Vitorbnc/ender3_addons/Laser Engraving Module/nubm08 laser diode pinout.png

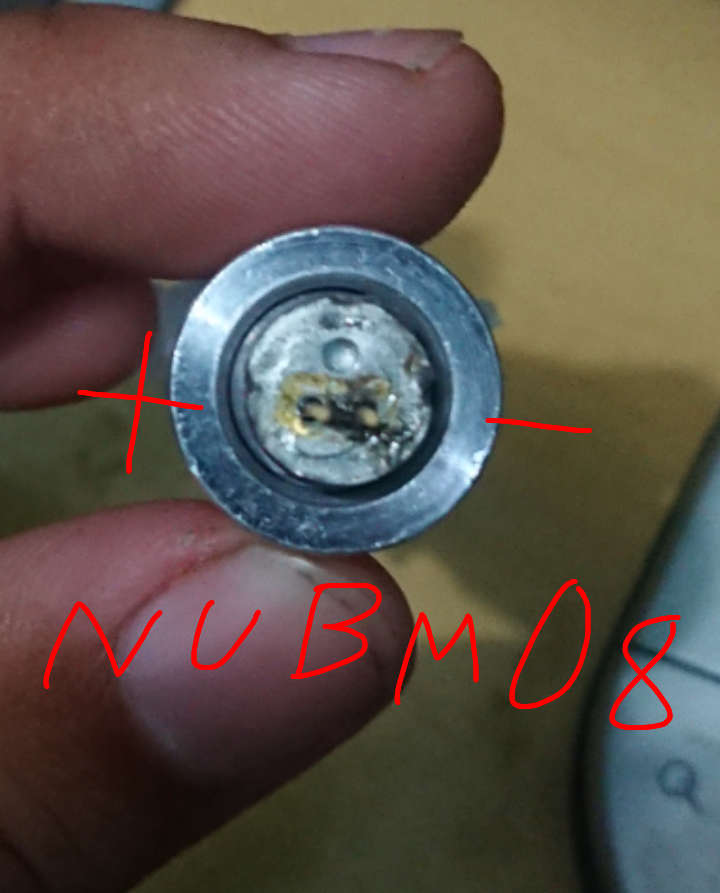
Laser Engraving Module/nubm08 laser diode pinout.png
