Vitorbnc/ender3_addons/Fresa CNC para Impressora 3D/broca pcb.jpg

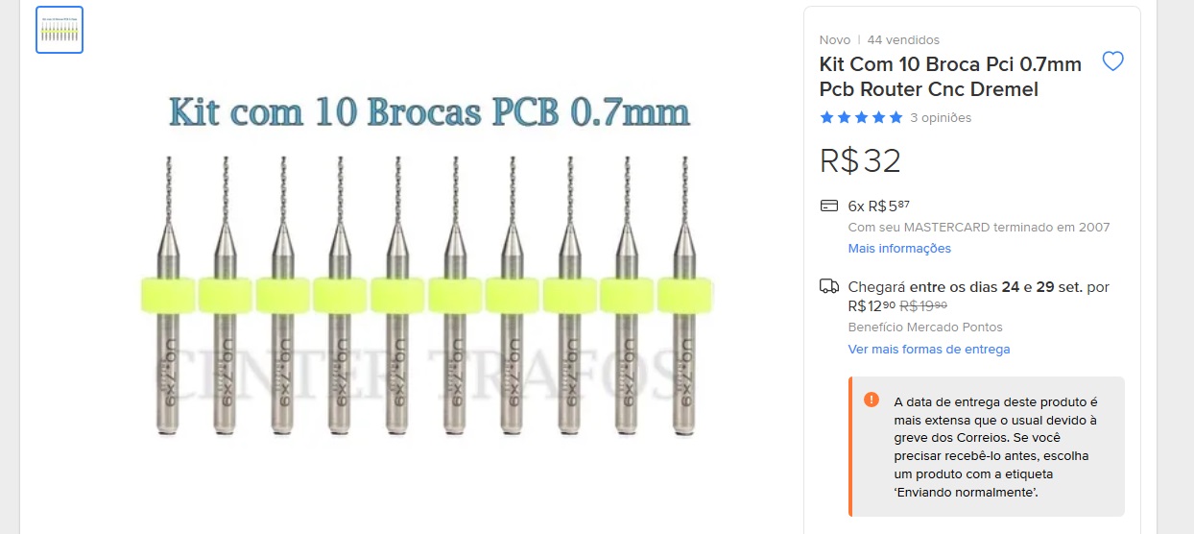
Fresa CNC para Impressora 3D/broca pcb.jpg
