Vitorbnc/ender3_addons/Fresa CNC para Impressora 3D/cnc tool home.png

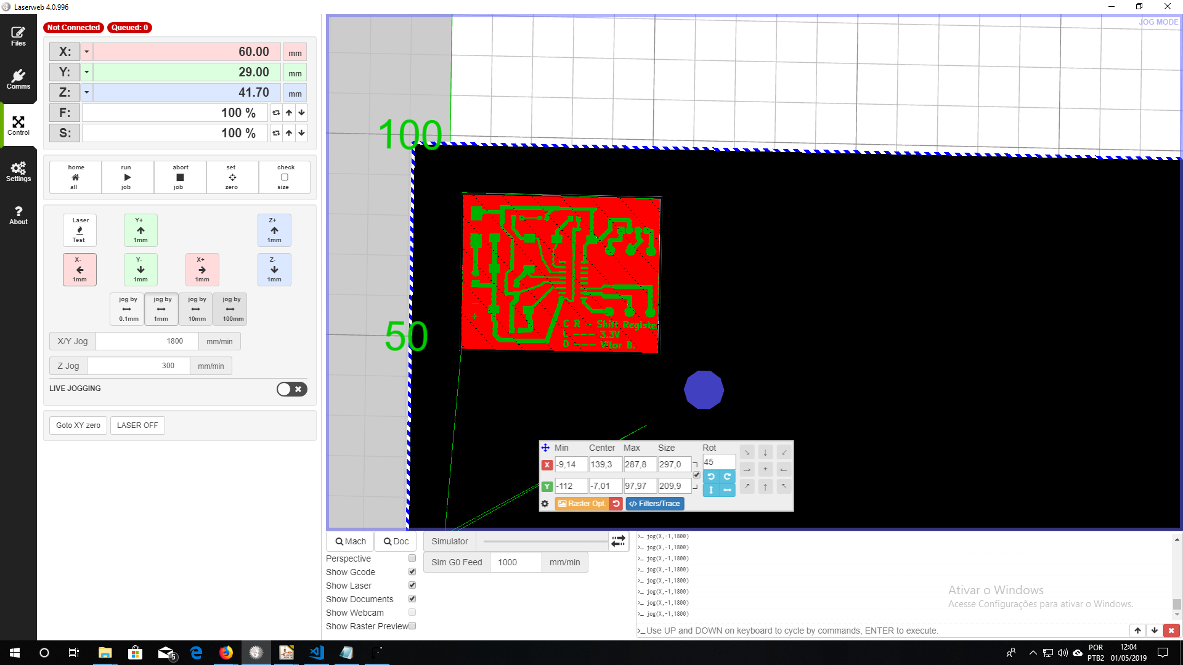
Fresa CNC para Impressora 3D/cnc tool home.png
