Vitorbnc/ender3_addons/Fresa CNC para Impressora 3D/compressor.png

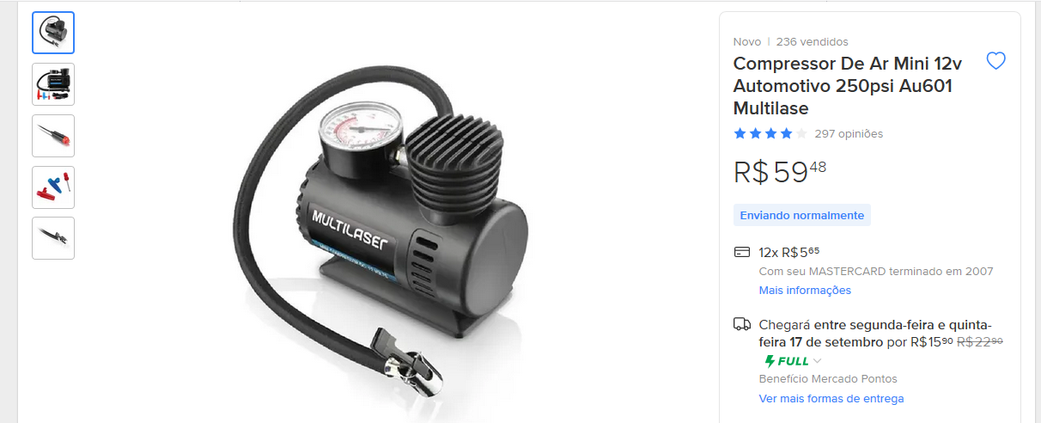
Fresa CNC para Impressora 3D/compressor.png
