Vitorbnc/ender3_addons/Fresa CNC para Impressora 3D/DSC_0071.JPG

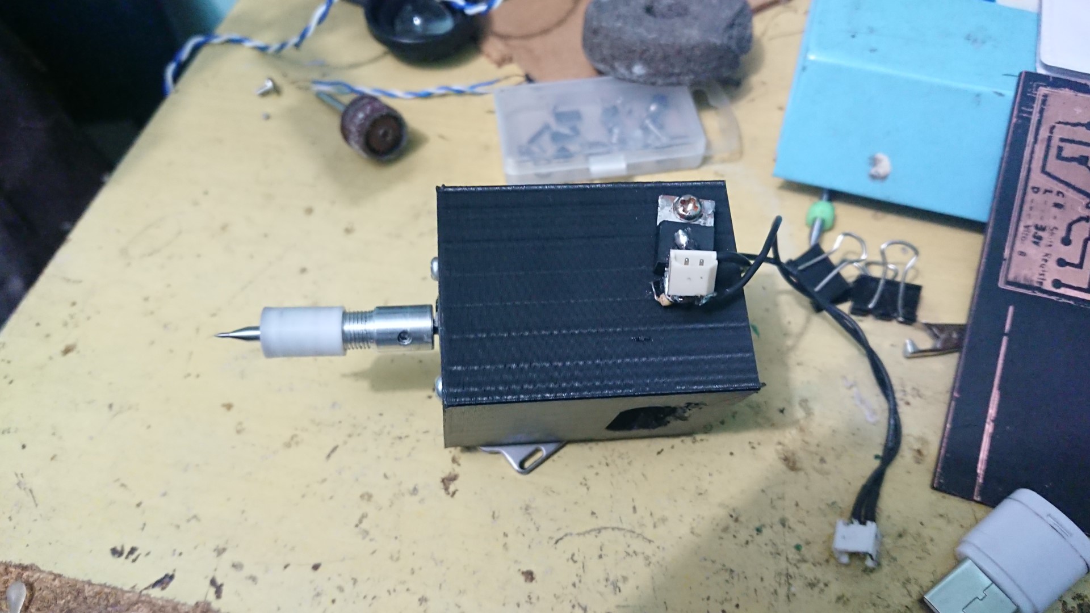
Fresa CNC para Impressora 3D/DSC_0071.JPG
