Vitorbnc/ender3_addons/Fresa CNC para Impressora 3D/DSC_0634.jpg

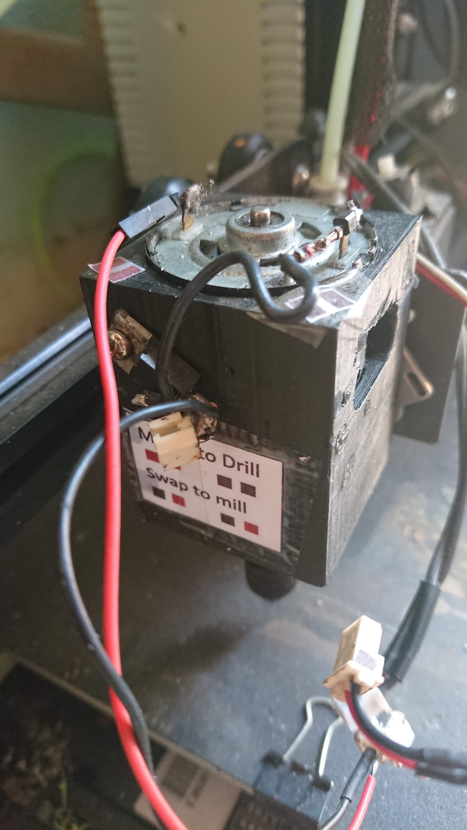
Fresa CNC para Impressora 3D/DSC_0634.jpg
