Vitorbnc/ender3_addons/Fresa CNC para Impressora 3D/Furos FlatCam/Flatcam settings.png

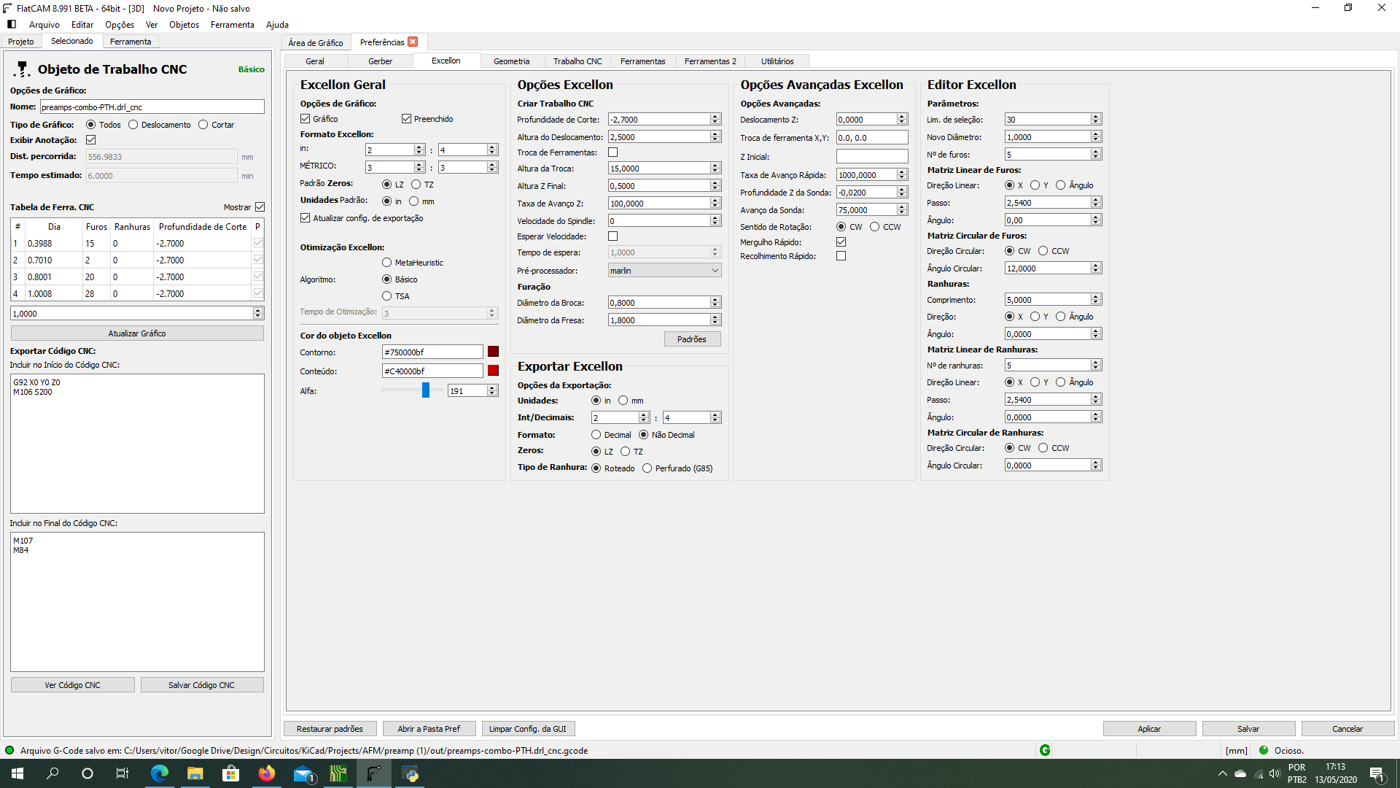
Fresa CNC para Impressora 3D/Furos FlatCam/Flatcam settings.png
