Vitorbnc/ender3_addons/Fresa CNC para Impressora 3D/generate drill file kicad.png

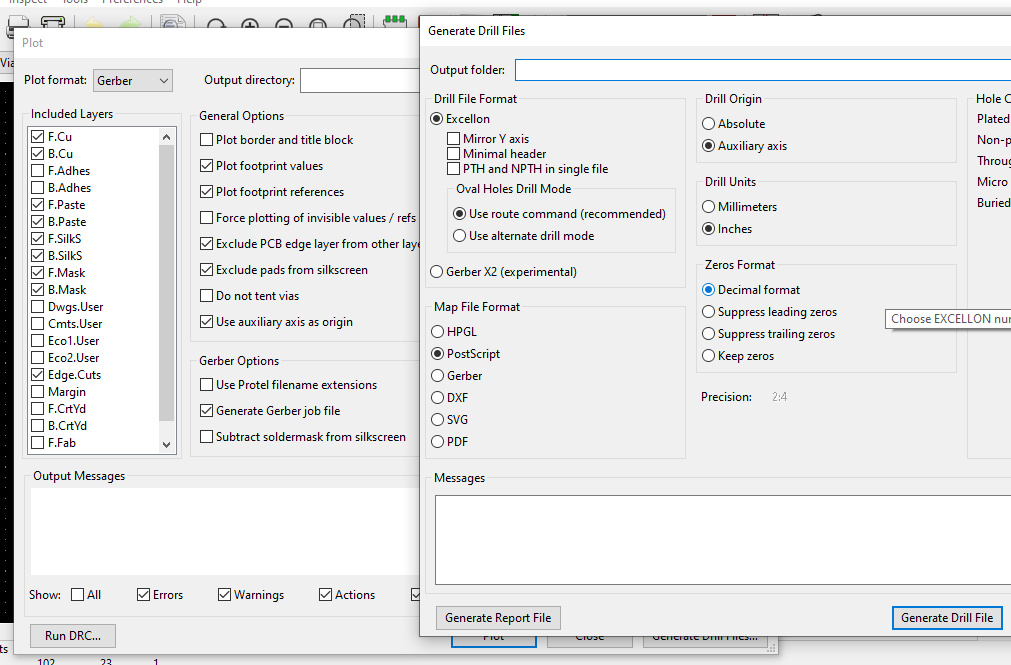
Fresa CNC para Impressora 3D/generate drill file kicad.png
