Vitorbnc/ender3_addons/Fresa CNC para Impressora 3D/import excellon flatcam.png

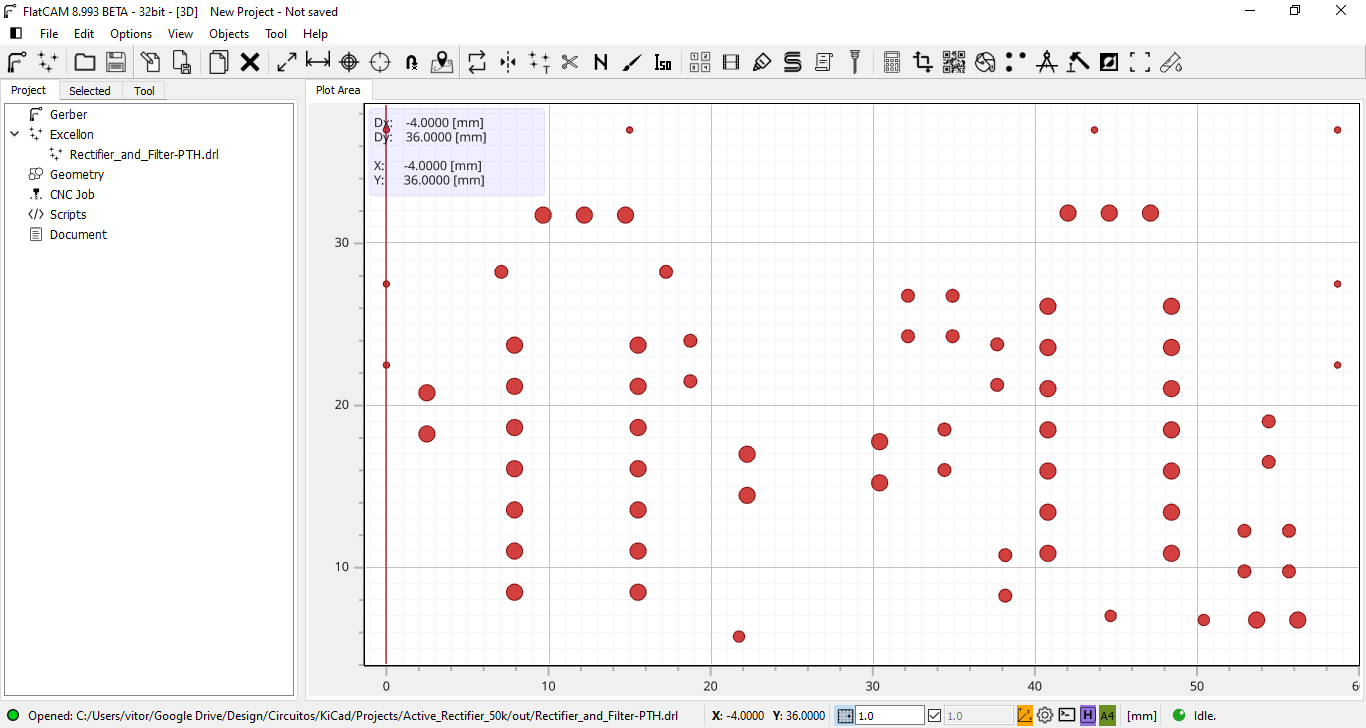
Fresa CNC para Impressora 3D/import excellon flatcam.png
