Vitorbnc/ender3_addons/Fresa CNC para Impressora 3D/mini mandril.png

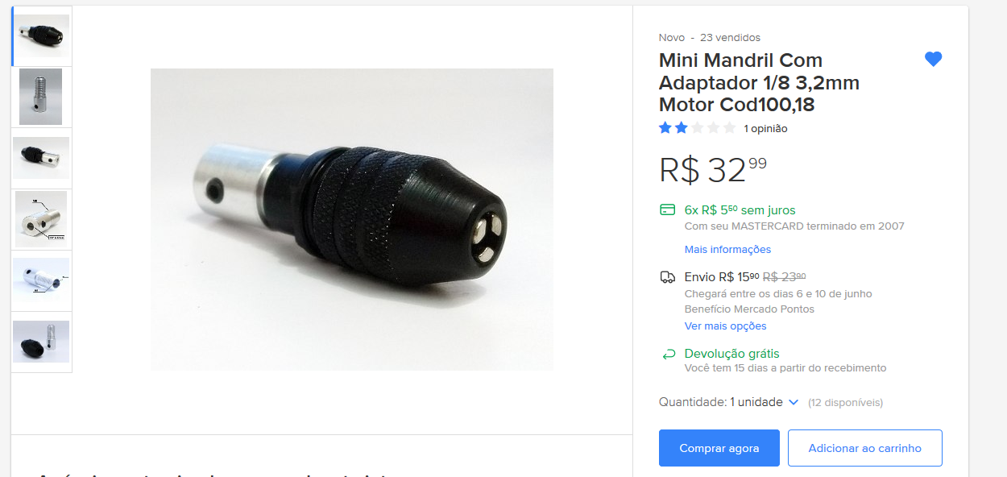
Fresa CNC para Impressora 3D/mini mandril.png
