Vitorbnc/ender3_addons/Fresa CNC para Impressora 3D/schematics.png

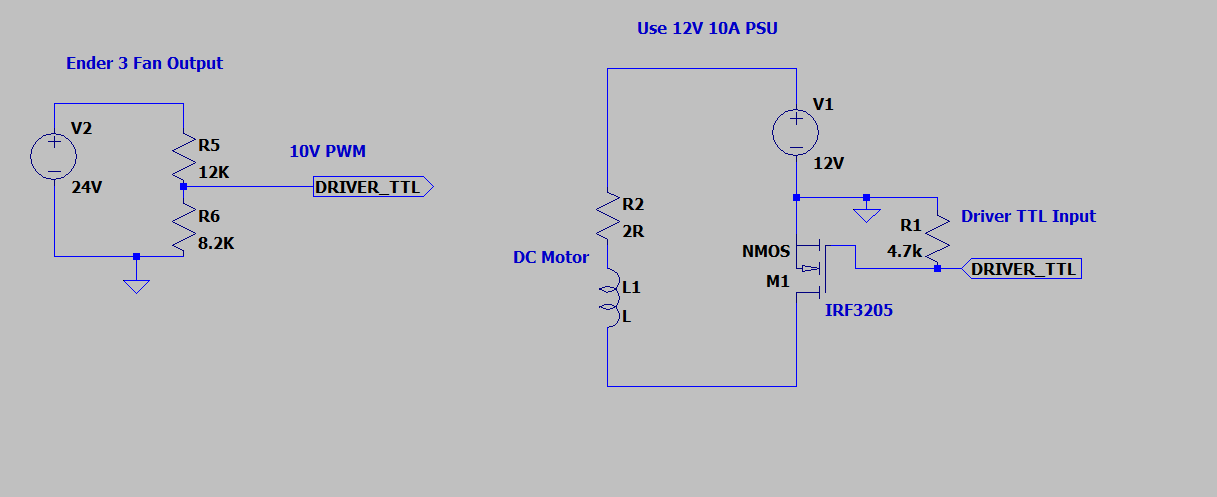
Fresa CNC para Impressora 3D/schematics.png
