Vitorbnc/ender3_addons/Laser Engraving Module/ender 3 laser pcb engraving zero position.png

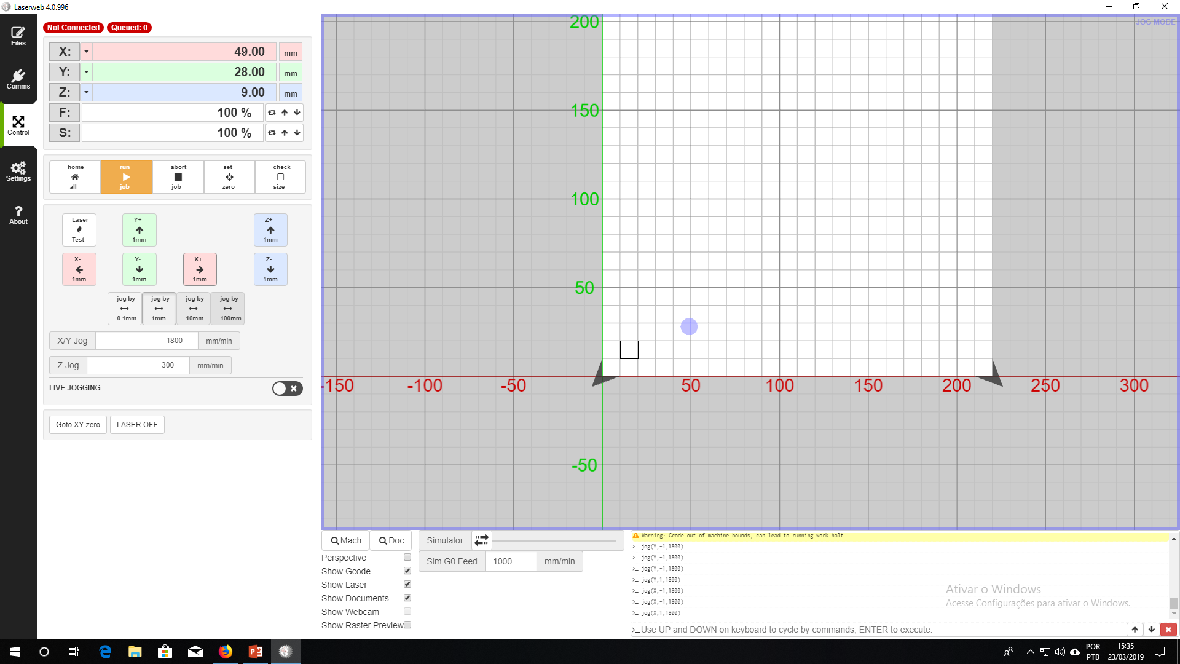
Laser Engraving Module/ender 3 laser pcb engraving zero position.png
