Vitorbnc/ender3_addons/Laser Engraving Module/Engraving Parameters/Params -  laser grbl madeira.png

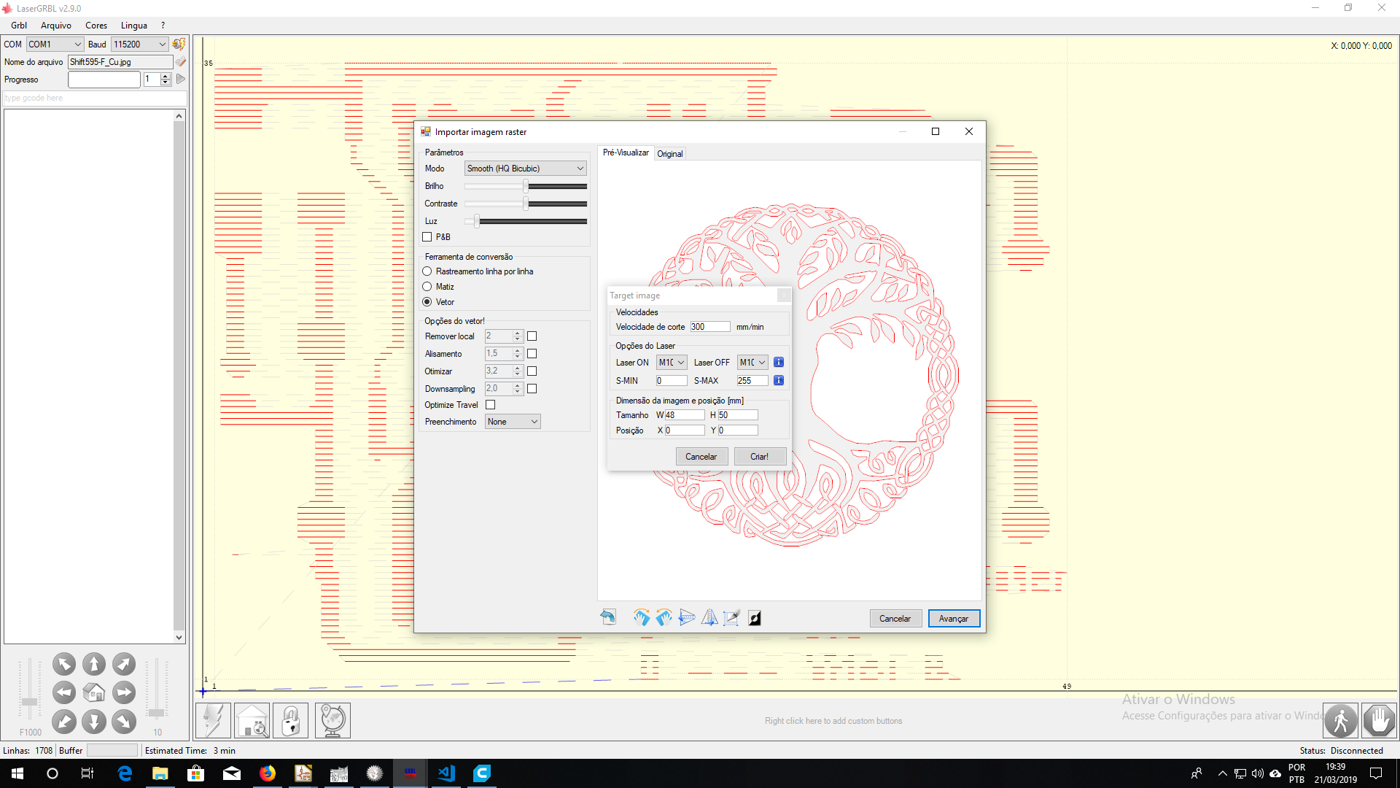
Laser Engraving Module/Engraving Parameters/Params - laser grbl madeira.png
