Vitorbnc/ender3_addons/Laser Engraving Module/Engraving Parameters/Params - gravação em plástico ou couro 2.png

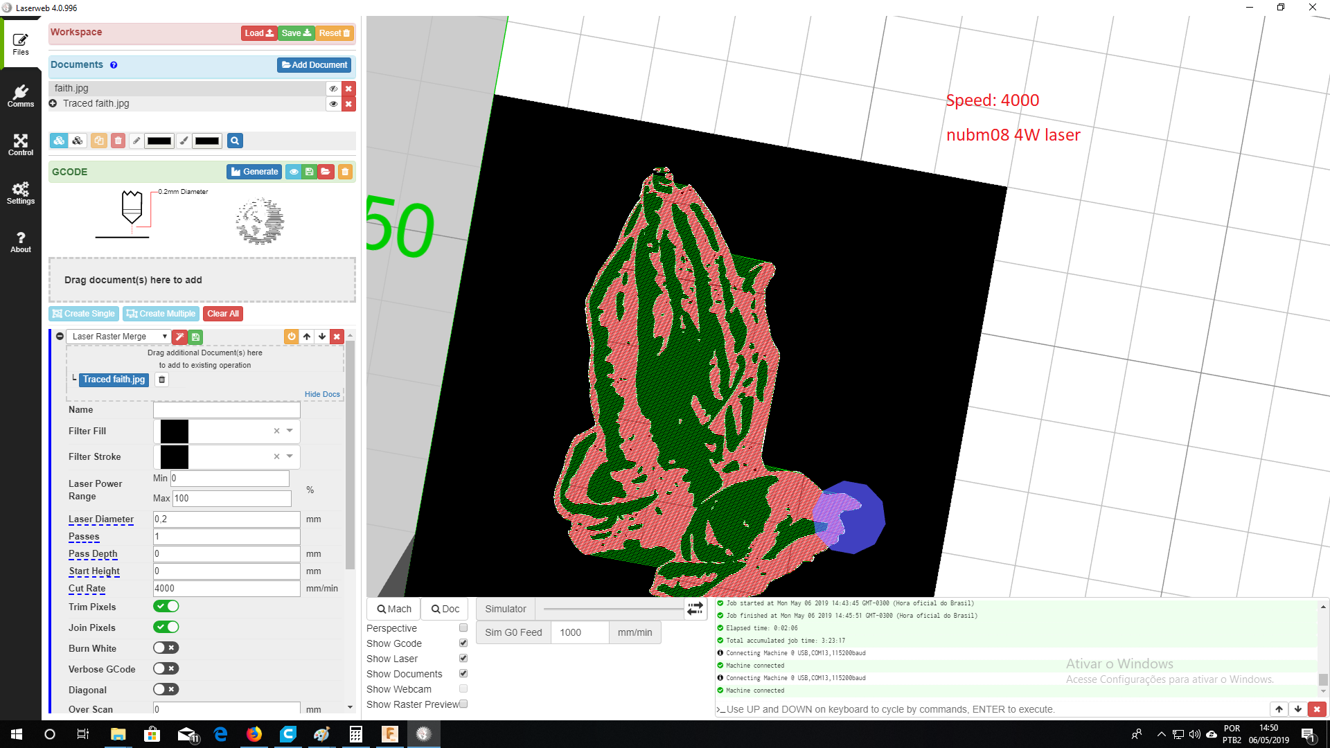
Laser Engraving Module/Engraving Parameters/Params - gravação em plástico ou couro 2.png
