Vitorbnc/ender3_addons/Laser Engraving Module/Engraving Parameters/Params - LaserWeb PCB Raster Settings.png

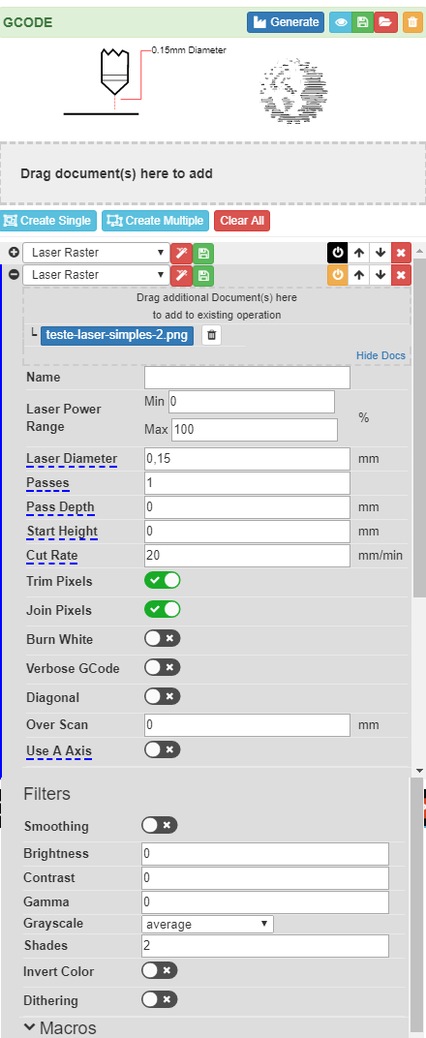
Laser Engraving Module/Engraving Parameters/Params - LaserWeb PCB Raster Settings.png
