Vitorbnc/ender3_addons/Laser Engraving Module/Fotos/Chaveamento com FET em paralelo - não mais usado.jpg

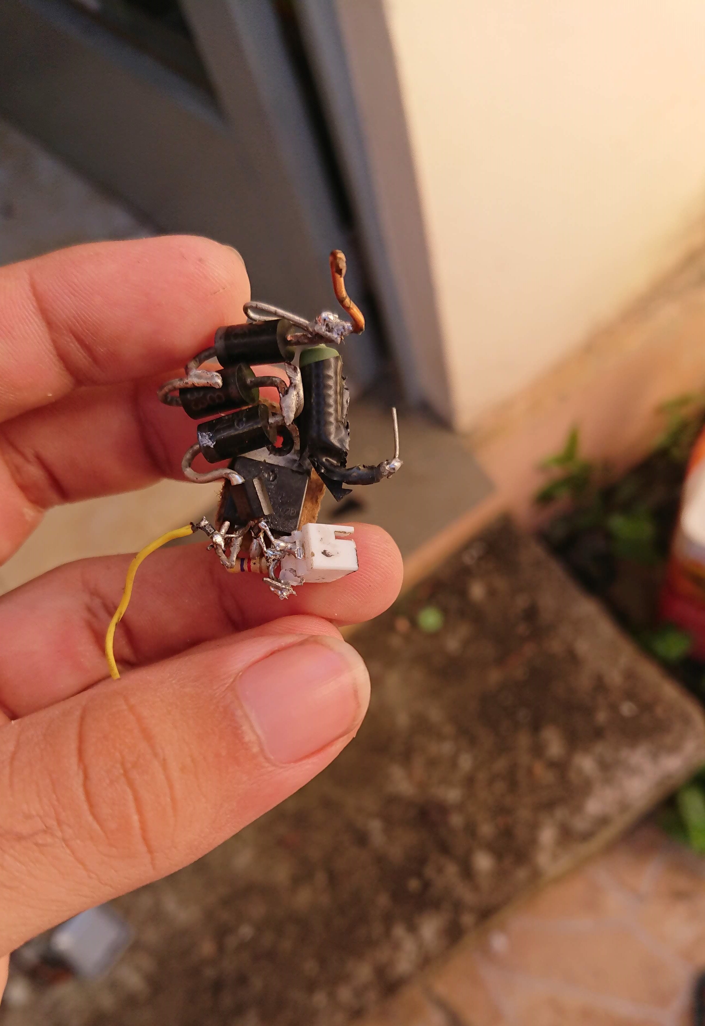
Laser Engraving Module/Fotos/Chaveamento com FET em paralelo - não mais usado.jpg
