Vitorbnc/ender3_addons/Laser Engraving Module/Fotos/DSC_0054.jpg

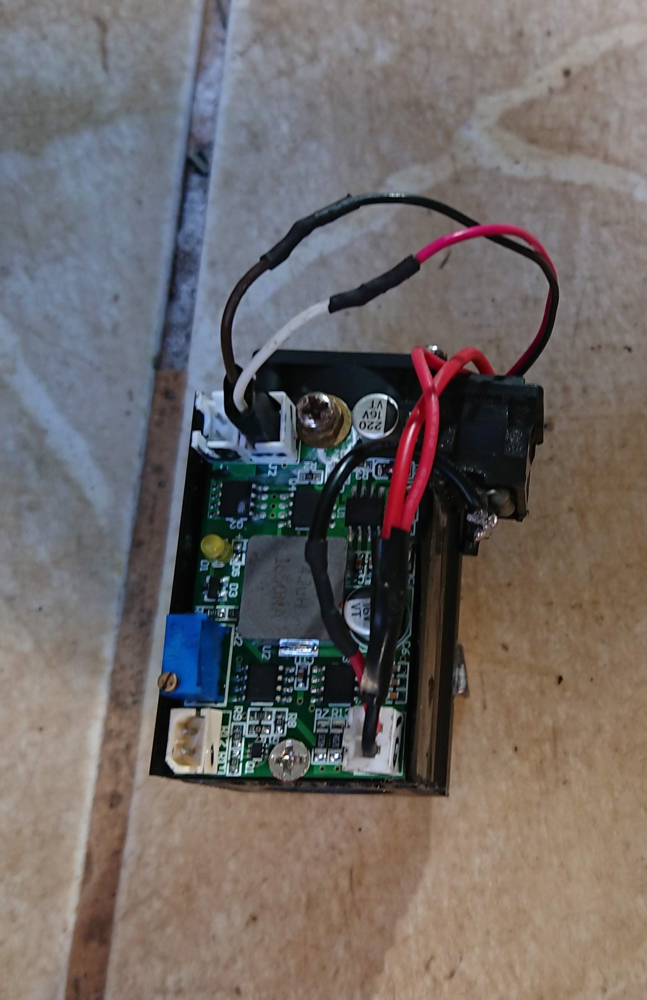
Laser Engraving Module/Fotos/DSC_0054.jpg
