Vitorbnc/ender3_addons/Laser Engraving Module/Fotos/DSC_0055.jpg

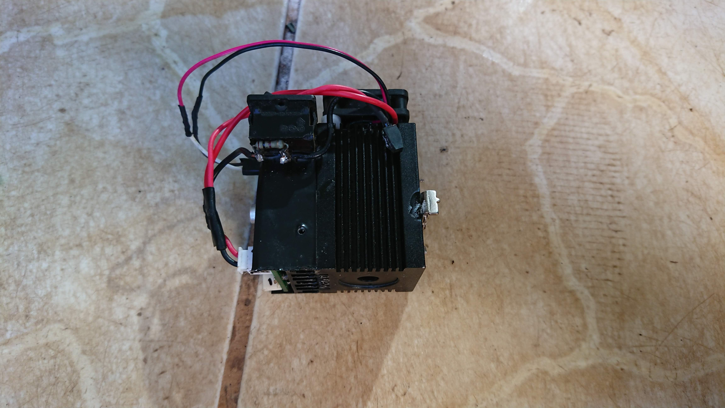
Laser Engraving Module/Fotos/DSC_0055.jpg
