Vitorbnc/ender3_addons/Laser Engraving Module/Fotos/DSC_0056.jpg

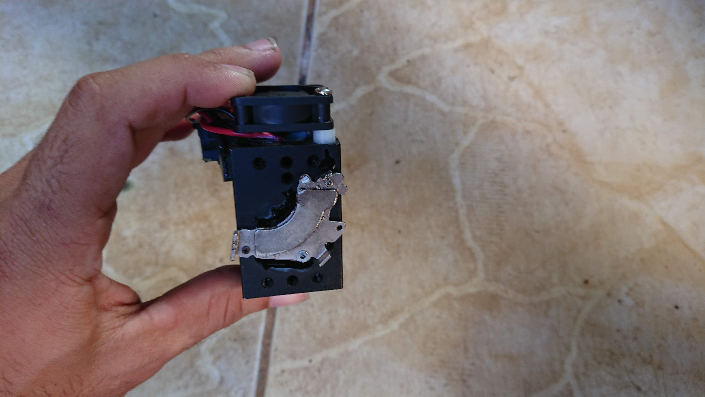
Laser Engraving Module/Fotos/DSC_0056.jpg
