Vitorbnc/ender3_addons/Laser Engraving Module/Fotos/DSC_0057.jpg

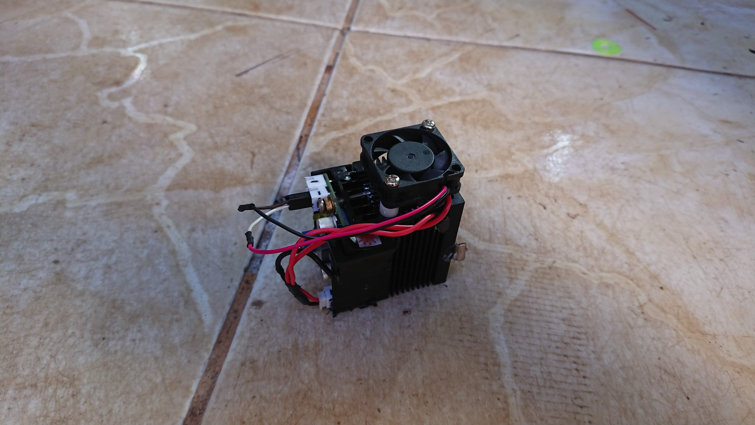
Laser Engraving Module/Fotos/DSC_0057.jpg
