Vitorbnc/ender3_addons/Laser Engraving Module/Fotos/version 2 (1).jpg

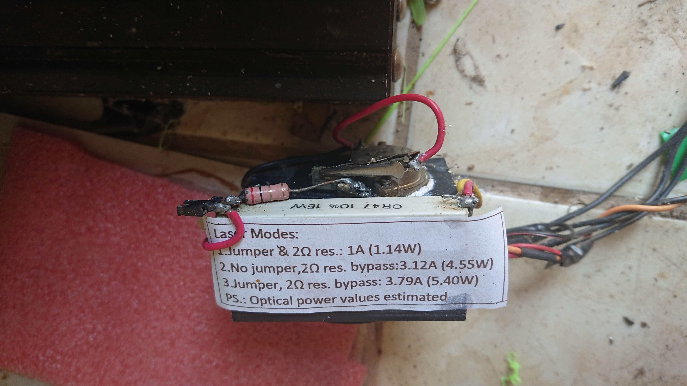
Laser Engraving Module/Fotos/version 2 (1).jpg
