Vitorbnc/ender3_addons/Laser Engraving Module/Gravação em Dry Film/Gravação em Dry Film PCB.JPG

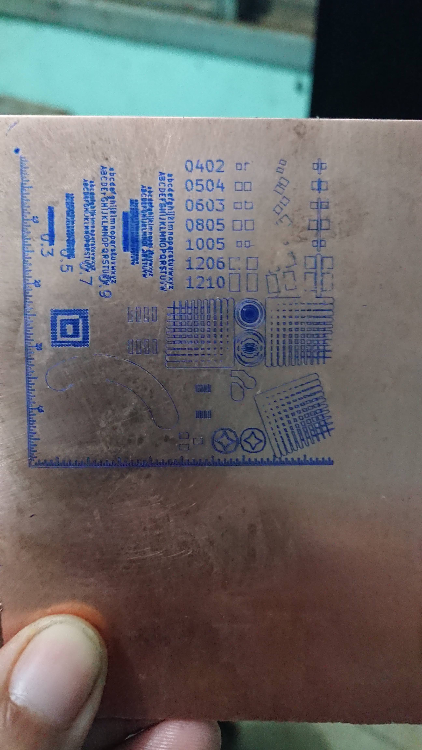
Laser Engraving Module/Gravação em Dry Film/Gravação em Dry Film PCB.JPG
