Vitorbnc/ender3_addons/Laser Engraving Module/Queimar tinta preta sobre PCB/Shift595 - Inf 1x 100, Sup - 1x200mmps - limpos.png

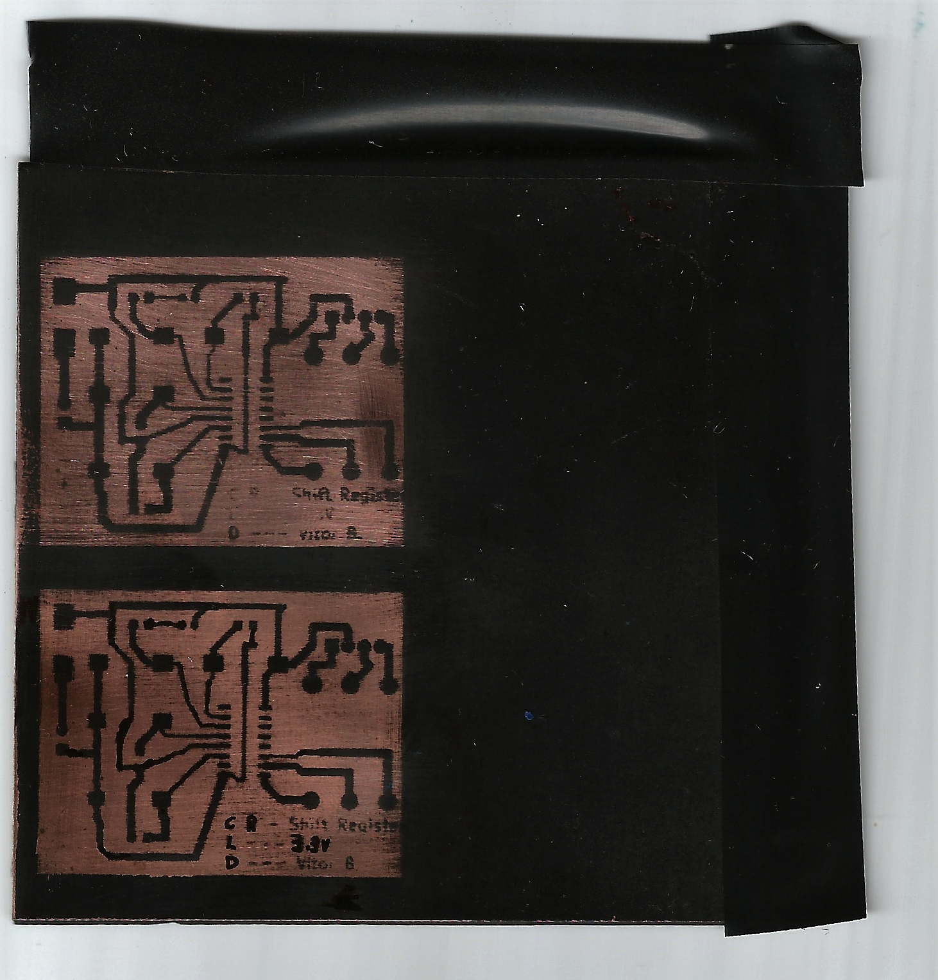
Laser Engraving Module/Queimar tinta preta sobre PCB/Shift595 - Inf 1x 100, Sup - 1x200mmps - limpos.png
