Vitorbnc/ender3_addons/Laser Engraving Module/Kit materiais laser.PNG

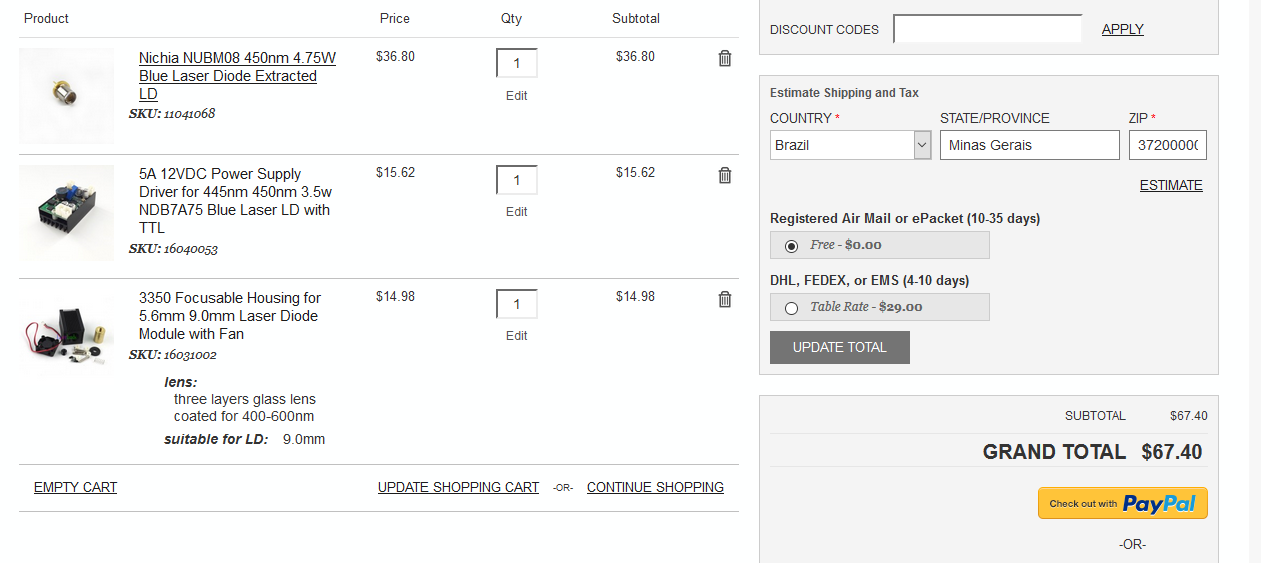
Laser Engraving Module/Kit materiais laser.PNG
