Vitorbnc/ender3_addons/Laser Engraving Module/Ender 3 Laser Wiring v1.png

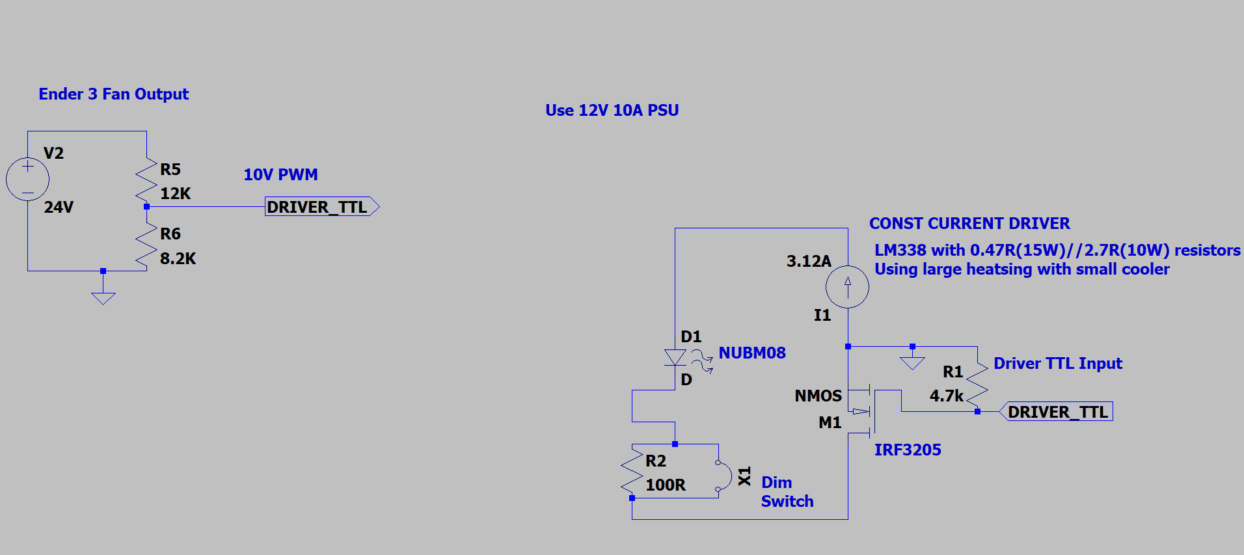
Laser Engraving Module/Ender 3 Laser Wiring v1.png
