Vitorbnc/ender3_addons/Laser Engraving Module/LEIA - Ender 3 Laser Wiring v1.png

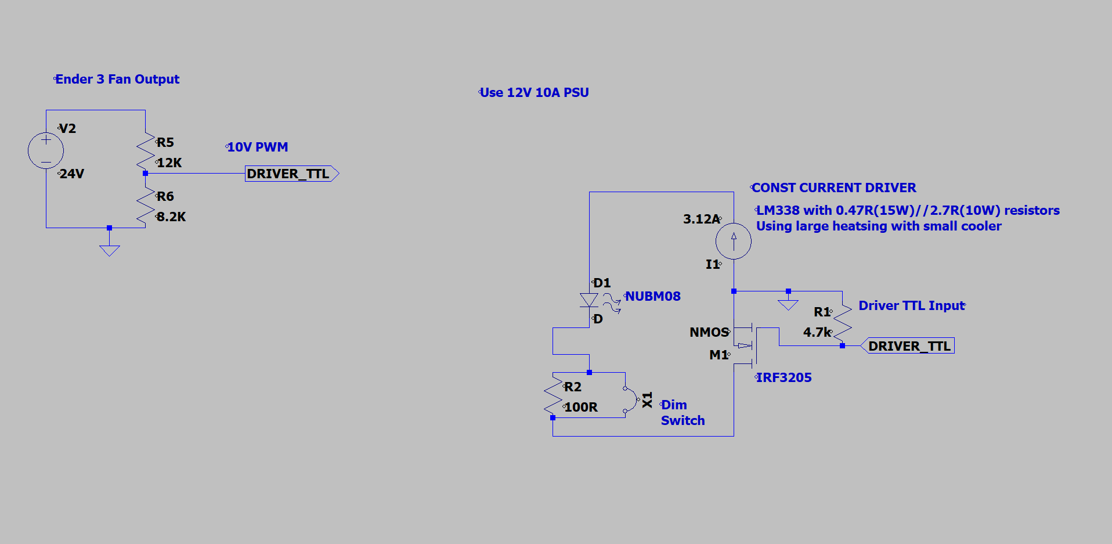
Laser Engraving Module/LEIA - Ender 3 Laser Wiring v1.png
