Vitorbnc/ender3_addons/Fresa CNC para Impressora 3D/teste_risca_tinta_pcb.JPG

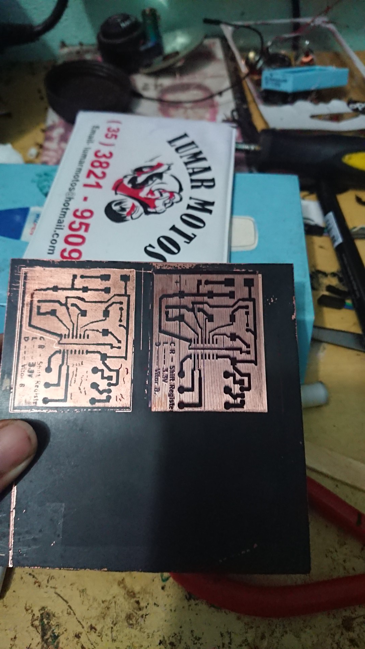
Fresa CNC para Impressora 3D/teste_risca_tinta_pcb.JPG
