Vitorbnc/ender3_addons/Laser Engraving Module/Imagens para teste/faith.jpg

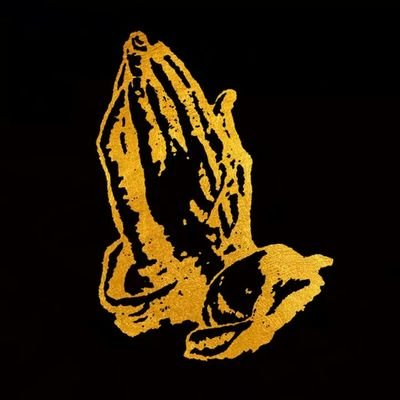
Laser Engraving Module/Imagens para teste/faith.jpg
