Vitorbnc/ender3_addons/Laser Engraving Module/Imagens para teste/yggdrasil.jpg

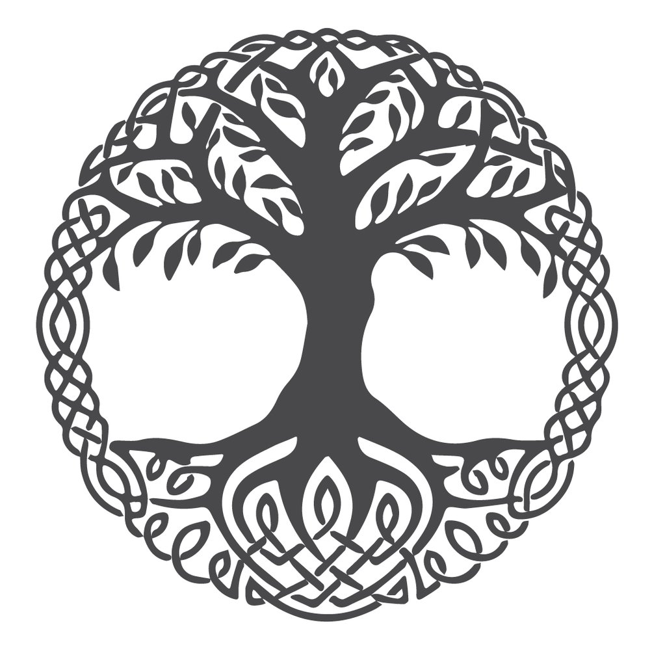
Laser Engraving Module/Imagens para teste/yggdrasil.jpg
