Vitorbnc/ender3_addons/Laser Engraving Module/NUBM08 Output Power x Current Test/anQD3n.jpg

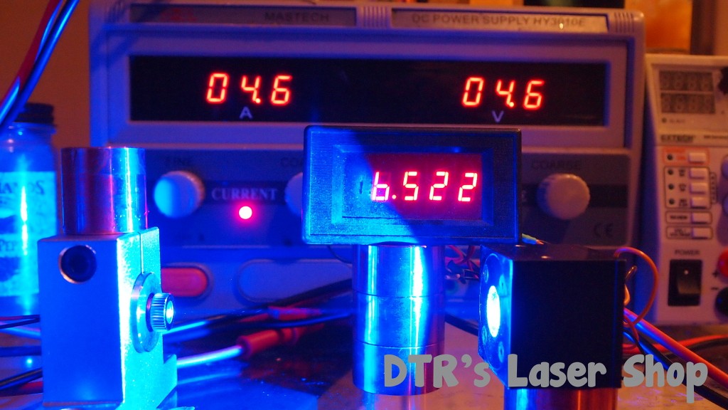
Laser Engraving Module/NUBM08 Output Power x Current Test/anQD3n.jpg
