Vitorbnc/ender3_addons/Laser Engraving Module/NUBM08 Output Power x Current Test/EfQZk6.jpg

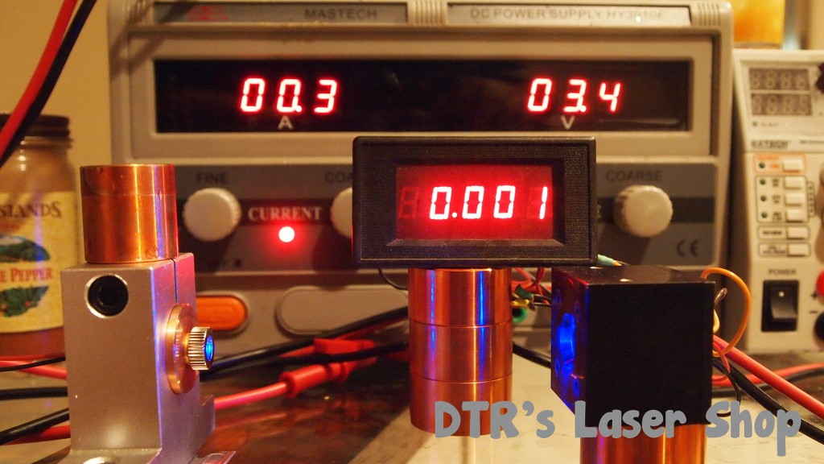
Laser Engraving Module/NUBM08 Output Power x Current Test/EfQZk6.jpg
