Vitorbnc/ender3_addons/Laser Engraving Module/Ender 3 Laser Wiring v1.asc

D1: LED
I1: current; 3.12A
M1: nmos
R1: res; 4.7k
R2: res; 100R; pwr=1
R5: res; 12K
R6: res; 8.2K
V2: voltage; 24V
X1: jumper
Named nets: 0, DRIVER_TTL
Dim
Switch
LM338 with 0.47R(15W)//2.7R(10W) resistors
Using large heatsing with small cooler
NUBM08
Ender 3 Fan Output
10V PWM
Use 12V 10A PSU
CONST CURRENT DRIVER
Driver TTL Input
IRF3205
