Vitorbnc/ender3_addons/Fresa CNC para Impressora 3D/schematics.asc

L1: ind
M1: nmos
R1: res; 4.7k
R2: res; 2R; pwr=1
R5: res; 12K
R6: res; 8.2K
V1: voltage; 12V
V2: voltage; 24V
Named nets: 0, DRIVER_TTL
Ender 3 Fan Output
10V PWM
Use 12V 10A PSU
Driver TTL Input
IRF3205
DC Motor
